svanheule/icecube-display/hardware/icecube-modular/strip_clip/clamp_back_top.scad

include <back_top.scad>;

back_top();
