svanheule/icecube-display/hardware/icecube-modular/strip_clip/clamp_front.scad

include <front.scad>;

front();
