svanheule/icecube-display/firmware/include/display_properties.h

#ifndef DISPLAY_PROPERPTIES_H
#define DISPLAY_PROPERPTIES_H

/** \file
  * \brief Device specific display properties.
  * \details As multiple LED configurations are supported, some definitions and functions need
  *   to be provided in order for the firmware to determine how to drive the display.
  *   For platform dependent properties, see device_properties.h.
  * \author Sander Vanheule (Universiteit Gent)
  */

#include <stdint.h>
#include "memspace.h"
#include "util/tlv_list.h"

/** \page display_metadata Display metadata reports
  * Display metadata can be requested over USB as a type-length-value list by sending a
  * \ref VENDOR_REQUEST_DISPLAY_PROPERTIES "DISPLAY_PROPERTIES" request
  * to the default control endpoint.
  * This is an easily extensible interface that can provide additional
  * information if future firmwares may require so.
  * An application like Steamshovel can use these metadata reports to automatically configure
  * which data to send to which display, using the correct buffer format.
  * With these reports different displays types can be supported without having to hard-code the
  * specific configuration of each existing device in the application.
  *
  * ## Report examples
  * ### IceTop display
  * A typical IceTop display TLV list looks as follows:
  * * ::DP_LED_TYPE (length 1): ::LED_TYPE_APA102
  * * ::DP_INFORMATION_TYPE (length 1): ::INFORMATION_IT_STATION
  * * ::DP_INFORMATION_RANGE (length 2): {1, 78}
  *
  * This implies that LED display consist of APA102 LEDs, which means 4 bytes of information
  * should be provided per LED.
  * The information that is displayed corresponds to IceTop stations, so the pulses from
  * DOMs 61-64 should be merged to determine the LED's color and brightness.
  * The (inclusive) range of supported IceTop stations is 1-78, so a full display frame consists
  * of \f$4 \times 78=312\f$ bytes.
  *
  * ### IceCube display
  * The \f$(2m)^3\f$ IceCube display consists of three modules.
  * A report of the center module may look as follows:
  * * ::DP_LED_TYPE (length 1): ::LED_TYPE_WS2811
  * * ::DP_INFORMATION_TYPE (length 1): ::INFORMATION_IC_STRING
  * * ::DP_INFORMATION_RANGE (length 2): {31, 50}
  * * ::DP_INFORMATION_RANGE (length 2): {79, 86}
  *
  * This report describes the central part of the display/detector.
  * A frame for this display contains \f$ 3 \times 60 \times (20+8)=5040 \f$ bytes.
  * This is a lot more data than the IceTop display, but a 12Mbps USB port should stil be able
  * to deliver 25FPS.
  *
  * ## Communication example
  * The following example reads the display information from all connected devices using pyusb:
  * \include usb.py
  */

/** \brief Different display properties TLV types
  */
enum display_property_type_t {
  /// Information type, always length 1. See ::display_information_type_t
  /// Allowed only once per metadata report.
  DP_INFORMATION_TYPE = 1,
  /// Information range, always length 2: `{start, end}`.
  /// If multiple ranges are supported by a device, they must not overlap.
  /// The supported ranges can be reported in any order.
  /// The data buffers corresponding to each range must be sorted by the staring value of
  /// their supported range, and concatenated for tranmisson to form a single display buffer.
  DP_INFORMATION_RANGE = 2,
  /// Type of LED used in the display, always length 1. See ::display_led_type_t.
  /// Allowed only once per metadata report.
  DP_LED_TYPE = 3,
  /// Display frame buffer size. Allowed once per metadata report.
  /// Depends on the number of LEDs present and the [LED type](\ref ::display_led_type_t).
  /// This information is optional and should only be used to check the buffer size calculated
  /// from the LED type, information type, and information ranges.
  DP_BUFFER_SIZE = 4,
  /// Display grouping. Always length 16.
  /// The display controller should advertise which group it belongs to. To determine the
  /// group identifier the serial number of the controllers should be sorted and concatenated
  /// into a single string, delimited by '+' characters: e.g. "ICD-IC-001-0001+ICD-IC-001-0002".
  /// The group identifier is then given by the (binary value) of the MD5 hash of the identifier
  /// string encoded in UTF-8.
  /// This 128 bit value is stored as big-endian 16 byte integer.
  DP_GROUP_ID = 5
};

/// Type of information the display is capable of showing.
enum display_information_type_t {
  /// IceTop stations. Pulses from all 4 DOMs in the two tanks should be merged.
  /// The frame buffer should contain the required LED data per station, in increasing order
  /// as determined by the DP_INFORMATION_RANGE field of the display metadata:
  /// e.g. `{[station 1], [station 2], ...}`.
  INFORMATION_IT_STATION = 0,
  /// Full IceCube strings. 1:1 mapping of in-ice DOMs to LEDs.
  /// The frame buffer should contain all DOMs per string:
  /// e.g. `{[dom 1 of string 1], [dom 2 of string 1], ... , [dom 1 of string 2], ...}`.
  INFORMATION_IC_STRING = 1
};

/// Type of LED IC used in the display.
enum display_led_type_t {
  /// APA102 compatible. Data for each LED consists of 4 bytes: brightness + RGB.
  LED_TYPE_APA102 = 0,
  /// WS2811/WS2812 compatible. Data for each LED consists of 3 bytes: RGB.
  LED_TYPE_WS2811 = 1
};

/// Order in which the RGB bytes should be pushed out to the display.
enum display_led_color_order_t {
    LED_ORDER_RGB = 0
  , LED_ORDER_BRG = 1
  , LED_ORDER_GBR = 2
  , LED_ORDER_BGR = 3
  , LED_ORDER_RBG = 4
  , LED_ORDER_GRB = 5
};

/** \brief Initialise the display properties cache.
  * \details Some display properties are stored in EEPROM which results in slow responses if this
  *   information is requested frequently. Information like the display's number of LEDs is
  *   therefore cached in RAM by this function.
  */
void init_display_properties();

/** \brief Return the (cached) number of LEDs present in the display.
  * \details This function will return 0 before the cache is initialised,
  *   or -1 (0xFFFF) if the EEPROM has been left unprogrammed.
  * \return The number of LEDs present in the display, or 0 if init_display_properties() has not
  *   been called yet.
  */
uint16_t get_led_count();

/// Return the number of bytes required to store the display information for a single LED.
/// \see ::display_led_type_t
uint8_t get_led_size();

/// The order in which the RGB data should be transmitted per LED.
enum display_led_color_order_t get_color_order();

/** \brief Get a pointer to the TLV list stored in flash.
  * \details The list ends with a ::TLV_TYPE_END field to ensure proper functioning of
  *   get_tlv_list_length_P().
  */
const struct dp_tlv_item_t* get_display_properties_P();

#endif //DISPLAY_PROPERPTIES_H
