svanheule/icecube-display/firmware/icetop-atmega32u4/render.py

#!/usr/bin/python3

import time, threading, struct
from icetopdisplay import DisplayComUsb
from icetopdisplay import FormatAPA102 as LedFormat

class Renderer:
  def __init__(self, station_count, frame_rate=25):
    self._timer = None
    self.halt = True
    self._com = None
    self.interval = 1/frame_rate
    self._station_count = station_count

  def start(self, displaycom):
    self._halt = False
    self.frame_number = 0
    self.display_time = 0
    self._com = displaycom
    self._com.acquire()
    self._start_time = time.time()
    self._setup_next_frame()

  def cancel(self):
    self._halt = True
    if self._timer is not None:
      self._timer.cancel()
      self._timer = None
    self._com.release()
    self._com = None

  def _setup_next_frame(self):
    next_time = self._start_time + self.display_time + self.interval
    self._timer = threading.Timer(next_time - time.time(), self._send_next_frame)
    self._timer.start()
    self.display_time = self.frame_number*self.interval
    self.frame_number += 1

  def _send_next_frame(self):
    try:
      if not self._halt:
        self._setup_next_frame()
      data = self.next_frame()
      self._com.send_frame(data)
      # Set up next frame transmission
    except StopIteration:
      self.cancel()

  def next_frame(self):
    pass

class TestRenderer(Renderer):
  DECAY_LENGTH = 6

  def __init__(self, station_count, frame_rate=25):
    super().__init__(station_count, frame_rate)
    self.position = 0
    self.direction = 1

  # Render frames with decaying brightness
  def next_frame(self):
    data = numpy.zeros((self._station_count, 4))

    # Calculate LED brightness
    brightness = 0.5
    for tail in range(self.DECAY_LENGTH):
      led = self.position - self.direction*tail
      if led in range(self._station_count):
        data[led] = LedFormat.float_to_led_data([brightness]*3)
      brightness /= 2

    # Update frame number
    if self.position == self._station_count-1 and self.direction == 1:
      self.direction = -1
    elif self.position == 0 and self.direction == -1:
      self.direction = 1

    self.position = self.position + self.direction

    return data

import numpy
import colorsys

class EventRenderer(Renderer):
  TIME_STRETCH = 4e-3 # in s/ns
  TIME_RISE = 0.5 # in s
  TIME_DECAY = 3.5

  def __init__(self, filename, station_count, frame_rate=25, overview_time=3):
    super().__init__(station_count, frame_rate)
    stations, charges, times = numpy.loadtxt(filename, skiprows=1, unpack=True)

    self.min_charge = min(charges)
    self.max_charge = max(charges)
    # Normalise charges and compress for displayability
    charges = numpy.power(charges/self.max_charge, .3)

    # Calculate time offset from first station and scale real time to display time
    times = self.TIME_STRETCH*(times - min(times)) + self.TIME_RISE
    self.min_time = min(times)
    self.max_time = max(times)

    self.stations = {}
    for i,station in enumerate(stations):
      # Discard unsupported stations, standard is [1,78], in-fill is [79-81]
      if station <= self._station_count:
        self.stations[int(station)] = (charges[i], times[i])

    self.stop_time = max(times) + self.TIME_DECAY
    self.overview_time = overview_time

    self.tau = self.TIME_DECAY / numpy.log(2**9)
    self.colours = self.render_overview()
    self.overview_frame = [LedFormat.float_to_led_data(rgb) for rgb in self.colours]

  def led_value(self, q0, t0):
    # Hue from 0 (red) to 2/3 (blue)
    hue = 2.*(t0-self.min_time)/(3*(self.max_time-self.min_time))
    # Fully saturated
    saturation = 1.
    # Value/brightness according to normalised charge
    value = q0
    return numpy.array(colorsys.hsv_to_rgb(hue, saturation, value))

  def render_overview(self):
    data = numpy.zeros((self._station_count, 3))
    for led in range(self._station_count):
      station = led+1
      if station in self.stations:
        q0, t0 = self.stations[station]
        data[led] = self.led_value(q0, t0)

    return data

  def brightness_curve(self, t, t0):
    # Linear rise to max brightness in TIME_RISE
    # Exponential decay from max brightness to 0 in TIME_DECAY
    t = t-t0
    if t <= -self.TIME_RISE:
      return 0
    elif t <= 0:
      return 1 + t/self.TIME_RISE
    elif t <= self.TIME_DECAY:
      return numpy.exp(-t/self.tau)
    else:
      return 0

  def pre_render_event(self):
    pulse_format = "<HB4B"
    pulse_size = struct.calcsize(pulse_format)
    pulses = []
    for index,station in enumerate(self.stations):
      q0, t0 = self.stations[station]
      frame = int(25*(t0-self.TIME_RISE))
      led = station-1
      led_value = LedFormat.float_to_led_data(self.led_value(q0, t0))
      pulse = struct.pack(pulse_format, frame, led, *led_value)
      pulses.append(pulse)

    pulses = sorted(pulses, key=lambda pulse: pulse[0])
    result = bytearray()
    for pulse in pulses:
      result += pulse
    return result

  def next_frame(self):
    if self.display_time < self.stop_time:
      data = numpy.zeros((self._station_count, 4))
      for led in range(self._station_count):
        station = led+1
        if station in self.stations:
          q0, t0 = self.stations[station]
          data[led] = LedFormat.float_to_led_data(self.brightness_curve(self.display_time, t0)*self.colours[led])
      return data
    elif self.display_time < self.stop_time+self.overview_time:
      return self.overview_frame
    else:
      raise StopIteration


import sys
import signal

class RenderInterrupt:
  def __init__(self, renderer):
    self._renderer = renderer
    signal.signal(signal.SIGINT, self._handler)

  def _handler(self, signal, frame):
    self._renderer.cancel()

import argparse

if __name__ == "__main__":
  parser = argparse.ArgumentParser(description="Render an IceTop event")
  parser.add_argument("-t", "--test", action="store_true", help="Render test mode.")
  parser.add_argument(
      "-n", "--no-display"
    , action="store_true"
    , help="Don't display the rendered frames. Usefull in combination with `--output'"
  )
  parser.add_argument(
      "-f", "--file"
    , nargs=1
    , type=argparse.FileType('r')
    , help="Render the IceTop station information contained in FILE"
  )
  parser.add_argument(
      "-o", "--output"
    , nargs=1
    , type=argparse.FileType('wb')
    , help="Write a pre-rendered output to OUTPUT. See also `--no-display'."
  )
  parser.add_argument(
      "-l", "--led-count"
    , nargs=1
    , required=True
    , type=int
    , choices=[78,81]
    , help="Number of IceTop stations or LEDs. Must be 78 or 81."
  )

  args = parser.parse_args(sys.argv[1:])
  renderer = None

  if args.file is not None:
    renderer = EventRenderer(args.file[0].name, args.led_count[0])
    if args.output is not None:
      pre_render = renderer.pre_render_event()
      args.output[0].write(pre_render)
  elif args.test:
    renderer = TestRenderer(args.led_count[0])
  else:
    print("No renderer specified.")
    sys.exit(-1)

  if not args.no_display:
    disp = DisplayComUsb()

    if renderer is not None:
      RenderInterrupt(renderer)
      renderer.start(disp)

    # Acquire and clear display
    disp.acquire()
    disp.flush_buffer()
    disp.release()
