svanheule/icecube-display/src/serial.h

#ifndef SERIAL_H
#define SERIAL_H

#include <stdint.h>

// USART interrupt handling
#define COMMAND_FRAME 'A'
#define COMMAND_DEMO 'D'
#define COMMAND_TEST_RING 'R'
#define COMMAND_TEST_SNAKE 'S'
#define COMMAND_GET_ID 'I'
#define COMMAND_LOCAL_MODE 'L'

void init_serial_port();

// TODO Rename usart_state to something more appropriate
enum usart_state_t {
    USART_LOCAL_MODE
  , USART_WAIT
  , USART_FRAME
  , USART_DEMO
  , USART_TEST_RING
  , USART_TEST_SNAKE
  // TODO Add diagnostics
};

enum usart_state_t get_usart_state();

uint8_t is_remote_connected();

#endif
